ScatteredDrifter/Discovery_ortho/firmware/qmk-workspace/sohortho/keymaps/vial/config.h

/* SPDX-License-Identifier: GPL-2.0-or-later */

#pragma once

#define VIAL_KEYBOARD_UID {0x8F, 0x8F, 0x17, 0xF8, 0x27, 0x6D, 0xFD, 0x93}

#define VIAL_UNLOCK_COMBO_ROWS { 1, 1 }
#define VIAL_UNLOCK_COMBO_COLS { 0, 10 }
